jetty840/freelss/src/WebContent.cpp

/*
 ****************************************************************************
 *  Copyright (c) 2014 Uriah Liggett <freelaserscanner@gmail.com>           *
 *	This file is part of FreeLSS.                                           *
 *                                                                          *
 *  FreeLSS is free software: you can redistribute it and/or modify         *
 *  it under the terms of the GNU General Public License as published by    *
 *  the Free Software Foundation, either version 3 of the License, or       *
 *  (at your option) any later version.                                     *
 *                                                                          *
 *  FreeLSS is distributed in the hope that it will be useful,              *
 *  but WITHOUT ANY WARRANTY; without even the implied warranty of          *
 *  MERCHANTABILITY or FITNESS FOR A PARTICULAR PURPOSE.  See the           *
 *  GNU General Public License for more details.                            *
 *                                                                          *
 *   You should have received a copy of the GNU General Public License      *
 *   along with FreeLSS.  If not, see <http://www.gnu.org/licenses/>.       *
 ****************************************************************************
*/

#include "Main.h"
#include "WebContent.h"
#include "PresetManager.h"
#include "Setup.h"
#include "Laser.h"
#include "Camera.h"
#include "Progress.h"
#include "PlyWriter.h"
#include "Lighting.h"
#include "WifiConfig.h"

namespace freelss
{

// A warning is displayed if we have less than this amount of disk space available
const int WebContent::LOW_DISK_SPACE_MB = 1000;

const std::string WebContent::CSS = "\
<style type=\"text/css\">\
.menu2 {\
	float: left;\
	width: 650px;\
	height: 20px;\
    text-align: right;\
}\
body {\
	font-size: 20px;\
	font-family: Verdana, serif, Arial, Helvetica;\
	background-color: #aaa;\
	color: #ffffff;\
	text-shadow: #000000 2px 2px 2px;\
}\
A:link    {color: #ffffff; font-size: 22px; font-weight: bold; text-shadow: #000000 2px 2px 2px; text-decoration: none;}\
A:visited {color: #ffffff; font-size: 22px; font-weight: bold; text-shadow: #000000 2px 2px 2px; text-decoration: none;}\
A:hover   {color: #ffffff; font-size: 22px; font-weight: bold; text-shadow: #000000 2px 2px 2px; text-decoration: underline;}\
A:active  {color: #ffffff; font-size: 22px; font-weight: bold; text-shadow: #000000 2px 2px 2px; text-decoration: underline;}\
.submit {\
	height: 40px;\
	margin-bottom: 10px;\
	font-weight: bold;\
	font-size: 18px;\
	margin-right: 15px;\
}\
.controlSubmit {\
	width: 200px;\
	height: 40px;\
	margin-bottom: 10px;\
	font-weight: bold;\
	font-size: 18px;\
	margin-right: 15px;\
}\
.message {\
	text: rgb(255, 0, 0);\
	font-weight: bold;\
	font-size: 18px;\
}\
.submitContainer {\
	float: left;\
}\
.menu {\
	float: left;\
	width: 200px;\
	height: 30px;\
	background-color: #cae9ff;\
	border: solid 2px #1d5fa9;\
	padding-top: 10px;\
	padding-bottom: 5px;\
	margin-right: 20px;\
}\
.settingsText {\
	float: left;\
	width: 250px;\
}\
.settingsDescr{\
	font-size: 10px;\
	padding-bottom: 20px;\
}\
.settingsInput {\
	width: 150px;\
}\
.result {\
	margin-top: 10px;\
	padding-top: 10px;\
	padding-left: 10px;\
	display: inline-block;\
	vertical-align: middle;\
	background-color: rgb(200, 200, 200);\
	border: solid 2px #1d5fa9;\
	width: 625px;\
}\
.calDescr{\
	font-size: 10px;\
	padding-bottom: 20px;\
	width: 200px;\
}\
.cal1GenerateDebugDiv {\
	padding-bottom: 50px;\
}\
#deleteButton {\
	float: left;\
	padding-left: 10px;\
}\
#viewButton {\
	padding-left: 250px;\
}\
#error1 {\
	font-size: 40px;\
	font-family: Verdana, serif, Arial, Helvetica;\
	color: #ff0000;\
	text-shadow: #000000 2px 2px 2px;\
}\
#menuContainer {\
	width: 800px;\
	text-align: center;\
	padding-bottom: 50px;\
}\
#cal1ContentDiv {\
    margin-top: 75px;\
}\
#cal1ControlsDiv {\
	float: left;\
}\
#cal1ImageDiv {\
	float: none;\
	margin-top: 75px;\
}\
#outerImageDiv {\
	float: none;\
	margin-top: 75px;\
	width: 1296px;\
	height: 972px;\
	background-size: contain;\
	background-repeat: no-repeat;\
	background-image: url('skull.jpg');\
}\
#outerPresetDiv {\
	margin-top: 75px;\
	background-color: rgb(130, 130, 130);\
	width: 650px;\
	margin-bottom: 10px;\
	padding-top: 10px;\
}\
#presetTextDiv {\
	float: left;\
	padding-left: 25px;\
	padding-right: 12px;\
	padding-top: 5px;\
}\
</style>";

const std::string WebContent::JAVASCRIPT= "\
<script type=\"text/javascript\">\
var imageCount = 0;\
\
function endsWith(str, suffix) {\
    return str.indexOf(suffix, str.length - suffix.length) !== -1;\
}\
\
function startup1(){\
	setTimeout(updateImgImage, 1000);\
}\
function startup2(){\
	setTimeout(updateDivImage, 1000);\
}\
function updateImgImage(){\
	var img = document.getElementById('image');\
	img.src = 'camImageL_' + Math.random() + '.jpg';\
	imageCount = imageCount + 1;\
}\
function updateDivImage(){\
	var div = document.getElementById('outerImageDiv');\
	div.style.backgroundImage = \"url('camImageL_\" + Math.random() + \".jpg')\";\
	imageCount = imageCount + 1;\
	setTimeout(updateDivImage, 4000);\
}\
function centerTableClick(event)\
{\
	var pos_x = event.offsetX?(event.offsetX):event.pageX-document.getElementById('outerImageDiv').offsetLeft;\
	var pos_y = event.offsetY?(event.offsetY):event.pageY-document.getElementById('outerImageDiv').offsetTop;\
	window.location.href = 'cal3?y=' + pos_y;\
}\
function rightLaserClick(event) {\
    var pos_x = event.offsetX?(event.offsetX):event.pageX-document.getElementById('outerImageDiv').offsetLeft;\
    var pos_y = event.offsetY?(event.offsetY):event.pageY-document.getElementById('outerImageDiv').offsetTop;\
	window.location.href = 'cal4?rightLaserX=' + pos_x + '&rightLaserY=' + pos_y;\
}\
function leftLaserClick(event) {\
	var pos_x = event.offsetX?(event.offsetX):event.pageX-document.getElementById('outerImageDiv').offsetLeft;\
	var pos_y = event.offsetY?(event.offsetY):event.pageY-document.getElementById('outerImageDiv').offsetTop;\
	window.location.href = 'cal5?leftLaserX=' + pos_x + '&leftLaserY=' + pos_y;\
}\
</script>";

const std::string WebContent::PROFILE_NAME = "PROFILE_NAME";
const std::string WebContent::SERIAL_NUMBER = "SERIAL_NUMBER";
const std::string WebContent::CAMERA_X = "CAMERA_X";
const std::string WebContent::CAMERA_Y = "CAMERA_Y";
const std::string WebContent::CAMERA_Z = "CAMERA_Z";
const std::string WebContent::CAMERA_MODE = "CAMERA_MODE";
const std::string WebContent::RIGHT_LASER_X = "RIGHT_LASER_X";
const std::string WebContent::RIGHT_LASER_Y = "RIGHT_LASER_Y";
const std::string WebContent::RIGHT_LASER_Z = "RIGHT_LASER_Z";
const std::string WebContent::RIGHT_LASER_PIN = "RIGHT_LASER_PIN";
const std::string WebContent::LEFT_LASER_X = "LEFT_LASER_X";
const std::string WebContent::LEFT_LASER_Y = "LEFT_LASER_Y";
const std::string WebContent::LEFT_LASER_Z = "LEFT_LASER_Z";
const std::string WebContent::LEFT_LASER_PIN = "LEFT_LASER_PIN";
const std::string WebContent::LASER_MAGNITUDE_THRESHOLD = "LASER_MAGNITUDE_THRESHOLD";
const std::string WebContent::LASER_ON_VALUE = "LASER_ON_VALUE";
const std::string WebContent::LASER_SELECTION = "LASER_SELECTION";
const std::string WebContent::STABILITY_DELAY = "STABILITY_DELAY";
const std::string WebContent::MAX_LASER_WIDTH = "MAX_LASER_WIDTH";
const std::string WebContent::MIN_LASER_WIDTH = "MIN_LASER_WIDTH";
const std::string WebContent::STEPS_PER_REVOLUTION = "STEPS_PER_REVOLUTION";
const std::string WebContent::ENABLE_PIN = "ENABLE_PIN";
const std::string WebContent::STEP_PIN = "STEP_PIN";
const std::string WebContent::DIRECTION_PIN = "DIRECTION_PIN";
const std::string WebContent::DIRECTION_VALUE = "DIRECTION_VALUE";
const std::string WebContent::RESPONSE_DELAY = "RESPONSE_DELAY";
const std::string WebContent::STEP_DELAY = "STEP_DELAY";
const std::string WebContent::FRAMES_PER_REVOLUTION = "FRAMES_PER_REVOLUTION";
const std::string WebContent::GENERATE_XYZ = "GENERATE_XYZ";
const std::string WebContent::GENERATE_STL = "GENERATE_STL";
const std::string WebContent::GENERATE_PLY = "GENERATE_PLY";
const std::string WebContent::SEPARATE_LASERS_BY_COLOR = "SEPARATE_LASERS_BY_COLOR";
const std::string WebContent::UNIT_OF_LENGTH = "UNIT_OF_LENGTH";
const std::string WebContent::VERSION_NAME = "VERSION_NAME";
const std::string WebContent::GROUND_PLANE_HEIGHT = "GROUND_PLANE_HEIGHT";
const std::string WebContent::PLY_DATA_FORMAT = "PLY_DATA_FORMAT";
const std::string WebContent::FREE_DISK_SPACE = "FREE_DISK_SPACE";
const std::string WebContent::ENABLE_BURST_MODE = "ENABLE_BURST_MODE";
const std::string WebContent::ENABLE_LIGHTING = "ENABLE_LIGHTING";
const std::string WebContent::LIGHTING_TYPE = "LIGHTING_TYPE";
const std::string WebContent::LIGHTING_PIN = "LIGHTING_PIN";
const std::string WebContent::LIGHTING_ILLUMINATION_RGB = "LIGHTING_ILLUMINATION_RGB";
const std::string WebContent::LIGHTING_LASER_RGB = "LIGHTING_LASER_RGB";
const std::string WebContent::LIGHTING_NETWORK_INDICATION = "LIGHTING_NETWORK_INDICATION";
const std::string WebContent::LIGHTING_NETWORK_INTERFACE = "LIGHTING_NETWORK_INTERFACE";
const std::string WebContent::CREATE_BASE_FOR_OBJECT = "CREATE_BASE_FOR_OBJECT";
const std::string WebContent::WIFI_ESSID = "WIFI_ESSID";
const std::string WebContent::WIFI_ESSID_HIDDEN = "WIFI_ESSID_HIDDEN";
const std::string WebContent::WIFI_PASSWORD = "WIFI_PASSWORD";
const std::string WebContent::KERNEL_VERSION = "KERNEL_VERSION";
const std::string WebContent::ENABLE_AUTHENTICATION = "ENABLE_AUTHENTICATION";
const std::string WebContent::AUTH_USERNAME = "AUTH_USERNAME";
const std::string WebContent::AUTH_PASSWORD1 = "AUTH_PASSWORD1";
const std::string WebContent::AUTH_PASSWORD2 = "AUTH_PASSWORD2";
const std::string WebContent::MENU2 = "<div class=\"menu2\"><a href=\"/checkUpdate\"><small><small>Check for Update</small></small></a>&nbsp;&nbsp;&nbsp;&nbsp;<a href=\"/network\"><small><small>Network</small></small></a>&nbsp;&nbsp;&nbsp;&nbsp;<a href=\"/security\"><small><small>Security</small></small></a>&nbsp;&nbsp;&nbsp;&nbsp;<a href=\"/setup\"><small><small>Setup</small></small></a></div>";


const std::string WebContent::SERIAL_NUMBER_DESCR = "The serial number of the ATLAS 3D scanner";
const std::string WebContent::CAMERA_X_DESCR = "X-compoment of camera location. ie: The camera is always at X = 0.";
const std::string WebContent::CAMERA_Y_DESCR = "Y-component of camera location. ie: The distance from camera center to the XZ plane";
const std::string WebContent::CAMERA_Z_DESCR = "Z-component of camera location. ie: The distance from camera center to origin";
const std::string WebContent::RIGHT_LASER_X_DESCR = "X coordinate of the right laser.  This is how far the laser is from the camera.";
const std::string WebContent::RIGHT_LASER_Y_DESCR = "Y coordinate of the right laser";
const std::string WebContent::RIGHT_LASER_Z_DESCR = "Z coordinate of the right laser.  The laser is parallel with the camera focal point";
const std::string WebContent::LEFT_LASER_X_DESCR = "X coordinate of the right laser.  This is how far the laser is from the camera.";
const std::string WebContent::LEFT_LASER_Y_DESCR = "Y coordinate of the right laser";
const std::string WebContent::LEFT_LASER_Z_DESCR = "Z coordinate of the right laser.  The laser is parallel with the camera focal point";
const std::string WebContent::LASER_MAGNITUDE_THRESHOLD_DESCR = "How bright the difference between a laser on and laser off pixel must be in order to be detected as part of the laser";
const std::string WebContent::RIGHT_LASER_PIN_DESCR = "The wiringPi pin number for controlling the right laser";
const std::string WebContent::LEFT_LASER_PIN_DESCR = "The wiringPi pin number for controlling the left laser";
const std::string WebContent::LASER_ON_VALUE_DESCR = "Set to 1 if setting the laser pin HIGH turns if on and 0 if LOW turns it on";
const std::string WebContent::STABILITY_DELAY_DESCR = "The time in microseconds to delay after moving the turntable and before taking a picture";
const std::string WebContent::MAX_LASER_WIDTH_DESCR = "Maximum laser width in pixels";
const std::string WebContent::MIN_LASER_WIDTH_DESCR = "Minimum laser width in pixels";
const std::string WebContent::STEPS_PER_REVOLUTION_DESCR = "The number of motor steps before the turntable spins 360 degrees";
const std::string WebContent::ENABLE_PIN_DESCR = "The wiringPi pin number for enabling the stepper motor";
const std::string WebContent::STEP_PIN_DESCR = "The wiringPi pin number for stepping the stepper motor";
const std::string WebContent::STEP_DELAY_DESCR = "The amount of time between steps in microseconds";
const std::string WebContent::DIRECTION_PIN_DESCR = "The wiringPi pin number for the stepper motor direction or rotation";
const std::string WebContent::RESPONSE_DELAY_DESCR = "The time it takes for the stepper controller to recognize a pin value change in microseconds";
const std::string WebContent::FRAMES_PER_REVOLUTION_DESCR = "The number of frames that should be taken for a scan. Default is 800.";
const std::string WebContent::GENERATE_XYZ_DESCR = "Whether to generate an XYZ point cloud file from the scan.";
const std::string WebContent::GENERATE_STL_DESCR = "Whether to generate an STL mesh from the scan.";
const std::string WebContent::GENERATE_PLY_DESCR = "Whether to generate a PLY point clould from the scan.";
const std::string WebContent::SEPARATE_LASERS_BY_COLOR_DESCR = "Calibration debugging option to separate the results from different lasers by color (requires PLY).";
const std::string WebContent::GROUND_PLANE_HEIGHT_DESCR = "Any scan data less than this height above the turntable will not be included in the output files.";
const std::string WebContent::PLY_DATA_FORMAT_DESCR = "Whether to generate binary or ASCII PLY files.";
const std::string WebContent::ENABLE_BURST_MODE_DESCR = "Enables the camera's burst mode when capturing in still mode";
const std::string WebContent::ENABLE_LIGHTING_DESCR = "Enables support for controlling a connected light.";
const std::string WebContent::LIGHTING_PIN_DESCR = "For type PWM, use The wiringPi pin number for the light. For type WS281x use the GPIO number (typically 18). Change will not go into effect until system is rebooted.";
const std::string WebContent::LIGHTING_ILLUMINATION_RGB_DESCR = "The RGB value used to illuminate the model when lasers are off during scanning, used for coloring the object.  Format RRGGBB (hex).  For type PWM; RR, GG and BB should be the same are represent intensity.";
const std::string WebContent::LIGHTING_LASER_RGB_DESCR = "The RGB value used to illuminate the model when lasers are on during scanning.  Format RRGGBB (hex).  For type PWM; RR, GG and BB should be the same are represent intensity.";
const std::string WebContent::CREATE_BASE_FOR_OBJECT_DESCR = "Adds a flat base to the object for easier 3D printing preparation.";
const std::string WebContent::WIFI_ESSID_DESCR = "The wireless network to configure";
const std::string WebContent::WIFI_PASSWORD_DESCR = "The password for the wireless network";
const std::string WebContent::ENABLE_AUTHENTICATION_DESCR = "Enables password protection for accessing the scanner";
const std::string WebContent::AUTH_USERNAME_DESCR = "The username to login with";
const std::string WebContent::AUTH_PASSWORD1_DESCR = "The password to login with";
const std::string WebContent::AUTH_PASSWORD2_DESCR = "Repeat the password";

std::string WebContent::scan(const std::vector<ScanResult>& pastScans)
{
	const Preset& preset = PresetManager::get()->getActivePreset();
	std::string presetName = preset.name;

	std::stringstream sstr;
	sstr << "<!DOCTYPE html><html><head>"
		 << CSS
		 << std::endl
		 << JAVASCRIPT
		 << std::endl
		 << "</head>"
	     << "\
<body>\
<div id=\"menuContainer\">\
  <div class=\"menu\"><a href=\"/\">SCAN</a></div>\
  <div class=\"menu\"><a href=\"/cal1\">CAMERA</a></div>\
  <div class=\"menu\"><a href=\"/settings\">SETTINGS</a></div>\
</div>\
<p>Click the button to start the scan </p>\
<form action=\"/\" method=\"POST\" enctype=\"application/x-www-form-urlencoded\">\
<div><div class=\"settingsText\">Preset</div><input class=\"settingsInput\" readonly=\"true\" value=\"" << presetName << "\"></div>\
<div><div class=\"settingsText\">Range</div><input name=\"degrees\" class=\"settingsInput\" value=\"360\"> degrees</div>\
	<input type=\"hidden\" name=\"cmd\" value=\"startScan\">\
	<input class=\"submit\" type=\"submit\" value=\"Start Scan\">\
</form>";

	int diskSpaceMb = GetFreeSpaceMb();
	if (diskSpaceMb < WebContent::LOW_DISK_SPACE_MB)
	{
		sstr << "<div id=\"error1\">LOW DISK SPACE WARNING: " << diskSpaceMb << " MB</div>";
	}

	for (size_t iRt = 0; iRt < pastScans.size(); iRt++)
	{
		sstr << WebContent::scanResult(iRt + 1, pastScans[iRt]);
	}

	sstr << "</body></html>";

	return sstr.str();
}

std::string WebContent::scanResult(size_t index, const ScanResult& result)
{
	std::stringstream sstr;

	time_t scanDate = result.getScanDate();

	struct tm * tp = localtime (&scanDate);
	std::string dateStr = asctime(tp);
	std::stringstream deleteUrl;

	std::stringstream thumbnail;
	thumbnail << "/dl/" << result.getScanDate() << ".png";
	deleteUrl << "/del?id=" << result.getScanDate();

	sstr << "<span>" << index << "\
	<div class=\"result\">\
	<div style=\"float: left\">\
	<img width=\"128\" border=\"0\" src=\"" << thumbnail.str() << "\">\
	</div>";

	bool hasPly = false;
	const std::vector<ScanResultFile>& files = result.files;
	for (size_t iFil = 0; iFil < files.size(); iFil++)
	{
		const ScanResultFile& file = files[iFil];
		if (file.extension != "png")
		{
			std::string upperExtension = file.extension;
			std::transform(upperExtension.begin(), upperExtension.end(), upperExtension.begin(), toupper);

			// Format the file size
			std::stringstream fileSize;
			if (file.fileSize > 1024 * 1024)
			{
				fileSize << file.fileSize / (1024 * 1024) << " MB";
			}
			else if (file.fileSize > 1024)
			{
				fileSize << file.fileSize / 1024 << " KB";
			}
			else
			{
				fileSize << file.fileSize << " B";
			}

			sstr << "&nbsp;<a href=\"/dl/" << result.getScanDate()
				 << "." << file.extension << "\">"
				 << upperExtension << "</a><small>&nbsp;["
				 << fileSize.str() << "]</small>";
		}

		if (file.extension == "ply")
		{
			hasPly = true;
		}
	}

	sstr << "<br><br>\
	<div id=\"deleteButton\"><form action=\"" << deleteUrl.str() << "#\" method=\"POST\">\
	<input type=\"Submit\" value=\"Delete\">\
	</form></div>";

	// Show the PLY view link
	if (hasPly)
	{
		sstr << "<div id=\"viewButton\"><form action=\"/view\" method=\"POST\" enctype=\"application/x-www-form-urlencoded\">"
			 << "<input type=\"Hidden\" name=\"id\" value=\"" << result.getScanDate() << "\">"
			 << "<input style=\"left-padding: 20px\" type=\"Submit\" value=\"View\">"
			 << "</form></div>";
	}

	sstr << "<div style=\"font-size: 12px\">" << dateStr << "\
	</div></div>\
	</span>\
	<br>";

	return sstr.str();
}

std::string WebContent::scanRunning(Progress& progress, real remainingTime)
{
	real minRemaining = remainingTime / 60.0;

	std::stringstream sstr;
	sstr << "<!DOCTYPE html><html><head>"
		 << "<meta http-equiv=\"refresh\" content=\"5\">"
		 << CSS
		 << std::endl
		 << JAVASCRIPT
		 << std::endl
		 << "</head>"
	     << "<body><p><div style=\"float: left\">"
	     << progress.getLabel()
	     << " is "
	     << progress.getPercent()
	     << "% complete";

		if (minRemaining > 0.01)
		{
			 sstr << " with "
				  << minRemaining
				  << " minutes remaining";
		}

	sstr << ".&nbsp;</div><div style=\"padding-left: 50px\"><form action=\"/preview\" method=\"GET\" enctype=\"application/x-www-form-urlencoded\">"
		 << "<input type=\"submit\" value=\"Preview\">"
		 << "</form></div><br><br>"
	     << "<form action=\"/\" method=\"POST\" enctype=\"application/x-www-form-urlencoded\">"
	     << "<input type=\"hidden\" name=\"cmd\" value=\"stopScan\">"
	     << "<input type=\"submit\" value=\"Stop Scan\">"
	     << "</form>"
	     << "</body></html>";

	     return sstr.str();
}

std::string WebContent::viewScan(const std::string& plyFilename)
{
	std::stringstream sstr;
	sstr << "<!DOCTYPE html><html><head>"
		 << CSS
		 << std::endl
		 << JAVASCRIPT
		 << std::endl
		 << "\
		 </head><body>\
		 <div style=\"position: absolute; left: 10px; top: 10px\"> <a href=\"/\">Back</a>&nbsp;&nbsp;<a href=\"/preview\">Refresh</a></div>\
		 <script src=\"three.min.js\"></script>\
		 <script src=\"OrbitControls.js\"></script>\
		 <script src=\"PLYLoader.js\"></script>\
		 <script>\
		 var scene = new THREE.Scene();\
		var camera = new THREE.PerspectiveCamera( 30, window.innerWidth/window.innerHeight, 1.0, 10000 );\
		var controls;\
\
		var renderer = new THREE.WebGLRenderer({ alpha: true });\
		renderer.setSize( window.innerWidth, window.innerHeight );\
		renderer.setClearColor( 0x555555, 1);\
\
		document.body.appendChild( renderer.domElement );\
		window.addEventListener( 'resize', onWindowResize, false );\
\
		var loader = new THREE.PLYLoader();\
		loader.addEventListener( 'load', function ( event ) {\
			var geometry = event.content;\
			var pcMaterial = new THREE.PointCloudMaterial( {\
			size: 1.75,\
			vertexColors: THREE.VertexColors\
		} );\
			geometry.useColor = true;\
			var mesh = new THREE.PointCloud( geometry, pcMaterial );\
			scene.add( mesh );\
		} );";

		sstr << "loader.load( '" << plyFilename << "');";

		sstr << "\
		var cylHeight = 1;\
		var cylRadius = 6 * 25.4;\
		var cylGeometry = new THREE.CylinderGeometry( cylRadius, cylRadius, cylHeight, 64 );\
		var cylMaterial = new THREE.MeshBasicMaterial( {color: 0x222222 } );\
		var cylinder = new THREE.Mesh( cylGeometry, cylMaterial );\
		cylinder.translateY( -cylHeight/2 );\
		scene.add( cylinder );\
\
		var cylHeight2 = 8;\
		var cylRadius2 = 6 * 25.4;\
		var cylGeometry2 = new THREE.CylinderGeometry( cylRadius2, cylRadius2, cylHeight2, 64 );\
		var cylMaterial2 = new THREE.MeshBasicMaterial( { color: 0xaaaaaa } );\
		var cylinder2 = new THREE.Mesh( cylGeometry2, cylMaterial2 );\
		cylinder2.translateY( -cylHeight2/2 - cylHeight );\
		scene.add( cylinder2 );\
\
		camera.position.z = 350;\
		camera.position.y = 450;\
		controls = new THREE.OrbitControls( camera );\
		controls.maxDistance = 1000;\
\
		var render = function () {\
			requestAnimationFrame( render );\
			renderer.render(scene, camera);\
		};\
\
		render();\
\
		function onWindowResize() {\
			windowHalfX = window.innerWidth / 2;\
			windowHalfY = window.innerHeight / 2;\
			camera.aspect = window.innerWidth / window.innerHeight;\
			camera.updateProjectionMatrix();\
			renderer.setSize( window.innerWidth, window.innerHeight );\
		}\
	</script>";

	sstr << "</body></html>";

	return sstr.str();
}

std::string WebContent::cal1(const std::string& inMessage)
{
	std::string message = inMessage.empty() ? std::string("") : ("<h2>" + inMessage + "</h2>");

	std::stringstream sstr;
	sstr << "<!DOCTYPE html><html><head>"
		 << CSS
		 << std::endl
		 << JAVASCRIPT
		 << std::endl
		 << "</head>"
	     << "\
<body onload=\"startup1();\">\
<div id=\"menuContainer\">\
  <div class=\"menu\"><a href=\"/\">SCAN</a></div>\
  <div class=\"menu\"><a href=\"/cal1\">CAMERA</a></div>\
  <div class=\"menu\"><a href=\"/settings\">SETTINGS</a></div>\
</div>"
	     << message
         << "\
<div id=\"cal1ContentDiv\">\
  <div id=\"cal1ControlsDiv\">\
    <div class=\"cal1GenerateDebugDiv\">\
		<form action=\"/cal1\" method=\"POST\" enctype=\"application/x-www-form-urlencoded\">\
			<input name=\"cmd\" value=\"generateDebug\" type=\"hidden\">\
			<input style=\"height: 60px\" class=\"controlSubmit\" value=\"Test\" type=\"submit\">\
		</form>\
    </div>\
    <div class=\"cal1GenerateDebugDiv\">\
        <form action=\"/cal1\" method=\"POST\" enctype=\"application/x-www-form-urlencoded\"><input name=\"cmd\" value=\"calibrateLasers\" type=\"hidden\"><input class=\"controlSubmit\" value=\"Calibrate Lasers\" type=\"submit\"></form>\
        <div class=\"calDescr\">Line the front wall of the calibration item over the center of the turntable hole and click this button to calibrate the lasers.</div>\
    </div>";

	sstr << "\
	<form action=\"/cal1\" method=\"POST\" enctype=\"application/x-www-form-urlencoded\"><input name=\"cmd\" value=\"toggleLeftLaser\" type=\"hidden\"><input class=\"controlSubmit\" value=\"Toggle Left Laser\" type=\"submit\"></form>\
	<form action=\"/cal1\" method=\"POST\" enctype=\"application/x-www-form-urlencoded\"> <input name=\"cmd\" value=\"toggleRightLaser\" type=\"hidden\"> <input class=\"controlSubmit\" value=\"Toggle Right Laser\" type=\"submit\"> </form>\
	<form action=\"/cal1\" method=\"POST\" enctype=\"application/x-www-form-urlencoded\">  <input name=\"cmd\" value=\"disableMotor\" type=\"hidden\">  <input class=\"controlSubmit\" value=\"Disable Motor\" type=\"submit\">  </form>\
	<div>\
		<form action=\"/cal1\" method=\"POST\" enctype=\"application/x-www-form-urlencoded\">\
		<input name=\"cmd\" value=\"rotateTable\" type=\"hidden\">\
		<input name=\"degrees\" style=\"width: 75px\" class=\"settingsInput\" value=\"360\" type=\"text\">\
		<input class=\"submit\" style=\"width: 110px\" value=\"Rotate\" type=\"submit\">\
		</form>\
	</div>\
	<div class=\"calDescr\">Rotates the turntable in degrees.</div>\
  </div>\
<div style=\"position: relative\">\
	<div>\
		<img style=\"position: absolute\" onload=\"setTimeout(updateImgImage, 0);\" id=\"image\" width=\"1296\" src=\"camImageL_\""
	<< time(NULL)
	<< ".jpg\">\
	</div>\
</div>\
</div></body></html>";

	     return sstr.str();
}

std::string WebContent::showUpdate(SoftwareUpdate * update, const std::string& message)
{
	std::stringstream sstr;
	sstr << "<!DOCTYPE html><html><head>"
		 << CSS
		 << std::endl
		 << JAVASCRIPT
		 << std::endl
		 << "</head>"
		 << "\
<body>\
<div id=\"menuContainer\">\
  <div class=\"menu\"><a href=\"/\">SCAN</a></div>\
  <div class=\"menu\"><a href=\"/cal1\">CAMERA</a></div>\
  <div class=\"menu\"><a href=\"/settings\">SETTINGS</a></div>"
		 << WebContent::MENU2
		 << "\
</div><div style=\"padding-top: 50px\">";

	if (update != NULL)
	{
		sstr << "<p>Update Available: " << update->name << "</p>";
		sstr << "<div><form action=\"/applyUpdate\" method=\"POST\" enctype=\"application/x-www-form-urlencoded\">";
		sstr <<" <input type=\"submit\" name=\"applyUpdate\" value=\"Apply Update\">";
		sstr <<" <input type=\"hidden\" name=\"majorVersion\" value=\"" << update->majorVersion << "\">";
		sstr <<" <input type=\"hidden\" name=\"minorVersion\" value=\"" << update->minorVersion << "\">";
		sstr << "</form></div>";
	}
	else if (!message.empty())
	{
		sstr << "<h2>" << message << "</h2>";
	}
	else
	{
		sstr << "<h2>No updates available.</h2>";
	}

	sstr << "</div></body></html>";

	return sstr.str();
}

std::string WebContent::updateApplied(SoftwareUpdate * update, const std::string& message, bool success)
{
	std::stringstream sstr;
	sstr << "<!DOCTYPE html><html><head>"
		 << CSS
		 << std::endl
		 << JAVASCRIPT
		 << std::endl
		 << "</head>"
		 << "\
<body>\
<div id=\"menuContainer\">\
  <div class=\"menu\"><a href=\"/\">SCAN</a></div>\
  <div class=\"menu\"><a href=\"/cal1\">CAMERA</a></div>\
  <div class=\"menu\"><a href=\"/settings\">SETTINGS</a></div>"
		 << WebContent::MENU2
		 << "\
</div><div style=\"padding-top: 50px\">";

	sstr << "<h2>" << message << "</h2>";

	sstr << "</div></body></html>";

	return sstr.str();
}

std::string WebContent::security(const std::string& message)
{
	Setup * setup = Setup::get();

	std::stringstream sstr;
	sstr << "<!DOCTYPE html><html><head>"
		 << CSS
		 << std::endl
		 << JAVASCRIPT
		 << std::endl
		 << "</head>"
		 << "\
<body>\
<div id=\"menuContainer\">\
  <div class=\"menu\"><a href=\"/\">SCAN</a></div>\
  <div class=\"menu\"><a href=\"/cal1\">CAMERA</a></div>\
  <div class=\"menu\"><a href=\"/settings\">SETTINGS</a></div>"
		 << WebContent::MENU2
		 << "\
</div><div style=\"padding-top: 50px\">";

	if (!message.empty())
	{
		sstr << "<h2>" << message << "</h2>";
	}

	sstr << "<form action=\"/security\" method=\"POST\" enctype=\"application/x-www-form-urlencoded\">";
	sstr << checkbox(WebContent::ENABLE_AUTHENTICATION, "Require Password", setup->enableAuthentication, ENABLE_AUTHENTICATION_DESCR);
	sstr << setting(WebContent::AUTH_USERNAME, "Username", "pi", AUTH_USERNAME_DESCR,  "", true);
	sstr << setting(WebContent::AUTH_PASSWORD1, "Password", "", AUTH_PASSWORD1_DESCR,  "", false, true);
	sstr << setting(WebContent::AUTH_PASSWORD2, "Repeat Password", "", AUTH_PASSWORD2_DESCR,  "", false, true);
	sstr << "<p><input type=\"hidden\" name=\"cmd\" value=\"save\">\
<input class=\"submit\" type=\"submit\" value=\"Save\">\
</p></form></div>\
</body></html>";

	return sstr.str();
}
std::string WebContent::network(const std::string& message, bool hiddenEssidInput)
{
	WifiConfig * wifi = WifiConfig::get();

	//  Perform a scan
	if (!hiddenEssidInput)
	{
		wifi->scan();
	}

	std::vector<std::string> interfaces = wifi->getAllInterfaces();
	std::vector<WifiConfig::AccessPoint> accessPoints = wifi->getAccessPoints();

	std::stringstream sstr;
	sstr << "<!DOCTYPE html><html><head>"
		 << CSS
		 << std::endl
		 << JAVASCRIPT
		 << std::endl
		 << "</head>"
		 << "\
<body>\
<div id=\"menuContainer\">\
  <div class=\"menu\"><a href=\"/\">SCAN</a></div>\
  <div class=\"menu\"><a href=\"/cal1\">CAMERA</a></div>\
  <div class=\"menu\"><a href=\"/settings\">SETTINGS</a></div>"
		 << WebContent::MENU2
		 << "\
</div><div style=\"padding-top: 50px\">";

	if (!message.empty())
	{
		sstr << "<h2>" << message << "</h2>";
	}

	sstr << "<form action=\"/network\" method=\"POST\" enctype=\"application/x-www-form-urlencoded\">";

	for (size_t iNt = 0; iNt < interfaces.size(); iNt++)
	{
		std::string interface = interfaces[iNt];
		if (interface != "lo")
		{
			sstr << setting(interface, interface, wifi->getIpAddress(interface), "IP address for " + interface, "", true);
		}
	}

	if (!hiddenEssidInput)
	{
		sstr << "<div><div class=\"settingsText\">Wireless Network</div>";
		sstr << "<select name=\"" << WebContent::WIFI_ESSID << "\">";
		for (size_t iAp = 0; iAp < accessPoints.size(); iAp++)
		{
			sstr << "<option value=\"" << iAp << "\">" << accessPoints[iAp].essid << "</option>\r\n";
		}

		sstr << "</select>&nbsp;&nbsp;<a href=\"?hidden=true\"><small><small>Hidden</small></small></a></div>";

		sstr << "";
		sstr << "<div class=\"settingsDescr\">" << WIFI_ESSID_DESCR << "</div>\n";
	}
	else
	{
		sstr << setting(WebContent::WIFI_ESSID_HIDDEN, "Wireless Network", "", WIFI_ESSID_DESCR);
	}

	sstr << setting(WebContent::WIFI_PASSWORD, "Wireless Password", "", WIFI_PASSWORD_DESCR);
	sstr << "<p><input type=\"hidden\" name=\"cmd\" value=\"connect\">\
<input class=\"submit\" type=\"submit\" value=\"Connect\">\
</p></form></div>\
</body></html>";

	return sstr.str();
}

std::string WebContent::setup(const std::string& message)
{
	const Setup * setup = Setup::get();
	UnitOfLength srcUnit = UL_MILLIMETERS; // Lengths are always represented in millimeters internally
	UnitOfLength dstUnit = setup->unitOfLength;

	// Detect the amount of free space available
	std::string freeSpaceMb = ToString(GetFreeSpaceMb());

	std::stringstream kernelVersion;
	struct utsname uts;

	if (uname(&uts) == 0)
	{
		kernelVersion << uts.sysname << " " << uts.release << " " << uts.version << " " << uts.machine;
	}

	std::stringstream sstr;
	sstr << "<!DOCTYPE html><html><head>"
		 << CSS
		 << std::endl
		 << JAVASCRIPT
		 << std::endl
		 << "</head>"
	     << "\
<body>\
<div id=\"menuContainer\">\
  <div class=\"menu\"><a href=\"/\">SCAN</a></div>\
  <div class=\"menu\"><a href=\"/cal1\">CAMERA</a></div>\
  <div class=\"menu\"><a href=\"/settings\">SETTINGS</a></div>"
	     << WebContent::MENU2
	     << "\
</div><div style=\"padding-top: 50px\">";

	if (!message.empty())
	{
		sstr << "<h2>" << message << "</h2>";
	}

	sstr << "<form action=\"/setup\" method=\"POST\" enctype=\"application/x-www-form-urlencoded\">";
	sstr << "<p><input class=\"submit\" type=\"submit\" value=\"Save\"></p>";

	sstr << setting(WebContent::SERIAL_NUMBER, "Serial Number", setup->serialNumber, SERIAL_NUMBER_DESCR);

	std::string mmSel = setup->unitOfLength == UL_MILLIMETERS ? " SELECTED" : "";
	std::string cmSel = setup->unitOfLength == UL_CENTIMETERS ? " SELECTED" : "";
	std::string inSel = setup->unitOfLength == UL_INCHES ? " SELECTED" : "";

	sstr << "<div><div class=\"settingsText\">Unit of Length</div>";
	sstr << "<select name=\"" << WebContent::UNIT_OF_LENGTH << "\">";
	sstr << "<option value=\"1\"" << mmSel << ">Millimeters</option>\r\n";
	sstr << "<option value=\"3\"" << cmSel << ">Centimeters</option>\r\n";
	sstr << "<option value=\"2\"" << inSel << ">Inches</option>\r\n";
	sstr << "</select></div>";
	sstr << "<div class=\"settingsDescr\">The unit of length for future values entered on the setup page.</div>\n";

	sstr << setting(WebContent::CAMERA_X, "Camera X", ConvertUnitOfLength(setup->cameraLocation.x, srcUnit, dstUnit), CAMERA_X_DESCR, ToString(dstUnit) + ".", true);
	sstr << setting(WebContent::CAMERA_Y, "Camera Y", ConvertUnitOfLength(setup->cameraLocation.y, srcUnit, dstUnit), CAMERA_Y_DESCR,  ToString(dstUnit) + ".");
	sstr << setting(WebContent::CAMERA_Z, "Camera Z", ConvertUnitOfLength(setup->cameraLocation.z, srcUnit, dstUnit), CAMERA_Z_DESCR,  ToString(dstUnit) + ".");
	sstr << setting(WebContent::RIGHT_LASER_X, "Right Laser X", ConvertUnitOfLength(setup->rightLaserLocation.x, srcUnit, dstUnit), RIGHT_LASER_X_DESCR,  ToString(dstUnit) + ".");
	sstr << setting(WebContent::RIGHT_LASER_Y, "Right Laser Y", ConvertUnitOfLength(setup->rightLaserLocation.y, srcUnit, dstUnit), RIGHT_LASER_Y_DESCR,  ToString(dstUnit) + ".", true);
	sstr << setting(WebContent::RIGHT_LASER_Z, "Right Laser Z", ConvertUnitOfLength(setup->rightLaserLocation.z, srcUnit, dstUnit), RIGHT_LASER_Z_DESCR,  ToString(dstUnit) + ".", true);
	sstr << setting(WebContent::LEFT_LASER_X, "Left Laser X", ConvertUnitOfLength(setup->leftLaserLocation.x, srcUnit, dstUnit), LEFT_LASER_X_DESCR,  ToString(dstUnit) + ".");
	sstr << setting(WebContent::LEFT_LASER_Y, "Left Laser Y", ConvertUnitOfLength(setup->leftLaserLocation.y, srcUnit, dstUnit), LEFT_LASER_Y_DESCR,  ToString(dstUnit) + ".", true);
	sstr << setting(WebContent::LEFT_LASER_Z, "Left Laser Z", ConvertUnitOfLength(setup->leftLaserLocation.z, srcUnit, dstUnit), LEFT_LASER_Z_DESCR,  ToString(dstUnit) + ".", true);

	sstr << setting(WebContent::RIGHT_LASER_PIN, "Right Laser Pin", setup->rightLaserPin, RIGHT_LASER_PIN_DESCR);
	sstr << setting(WebContent::LEFT_LASER_PIN, "Left Laser Pin", setup->leftLaserPin, LEFT_LASER_PIN_DESCR);
	sstr << setting(WebContent::LASER_ON_VALUE, "Laser On Value", setup->laserOnValue, LASER_ON_VALUE_DESCR);

	sstr << setting(WebContent::STEPS_PER_REVOLUTION, "Steps Per Revolution", setup->stepsPerRevolution, STEPS_PER_REVOLUTION_DESCR);
	sstr << setting(WebContent::ENABLE_PIN, "Motor Enable Pin", setup->motorEnablePin, ENABLE_PIN_DESCR);
	sstr << setting(WebContent::STEP_PIN, "Motor Step Pin", setup->motorStepPin, STEP_PIN_DESCR);
	sstr << setting(WebContent::STEP_DELAY, "Motor Step Delay", setup->motorStepDelay, STEP_DELAY_DESCR, "&mu;s");
	sstr << setting(WebContent::DIRECTION_PIN, "Motor Direction Pin", setup->motorDirPin, DIRECTION_PIN_DESCR);
	sstr << setting(WebContent::RESPONSE_DELAY, "Motor Response Delay", setup->motorResponseDelay, RESPONSE_DELAY_DESCR, "&mu;s");
	sstr << checkbox(WebContent::ENABLE_LIGHTING, "Enable Lighting", setup->enableLighting, ENABLE_LIGHTING_DESCR);

	std::string pwmSel = setup->lightingType == LT_PWM ? " SELECTED" : "";
	std::string ws281xSel = setup->lightingType == LT_WS281X ? " SELECTED" : "";

	sstr << "<div><div class=\"settingsText\">Lighting Type</div>";
	sstr << "<select name=\"" << WebContent::LIGHTING_TYPE << "\">";
	sstr << "<option value=\"1\"" << pwmSel << ">PWM</option>\r\n";
	sstr << "<option value=\"2\"" << ws281xSel << ">WS281x</option>\r\n";
	sstr << "</select></div>";
	sstr << "<div class=\"settingsDescr\">The type of lighting installed.  WS281x is also known as Neopixel.</div>\n";

	sstr << setting(WebContent::LIGHTING_PIN, "Lighting Pin", setup->lightingPin, LIGHTING_PIN_DESCR);
	sstr << setting(WebContent::LIGHTING_ILLUMINATION_RGB, "Lighting Illumination RGB", setup->lightingIlluminationRGB, LIGHTING_ILLUMINATION_RGB_DESCR);
	sstr << setting(WebContent::LIGHTING_LASER_RGB, "Lighting Laser RGB", setup->lightingLaserRGB, LIGHTING_LASER_RGB_DESCR);

	std::string offSel = setup->lightingNetworkIndication == LN_OFF ? " SELECTED" : "";
	std::string fullSel = setup->lightingNetworkIndication == LN_FULL ? " SELECTED" : "";
	std::string lastSel = setup->lightingNetworkIndication == LN_LAST ? " SELECTED" : "";

	sstr << "<div><div class=\"settingsText\">Lighting Network IP Indication</div>";
	sstr << "<select name=\"" << WebContent::LIGHTING_NETWORK_INDICATION << "\">";
	sstr << "<option value=\"1\"" << offSel << ">Off</option>\r\n";
	sstr << "<option value=\"2\"" << fullSel << ">Full</option>\r\n";
	sstr << "<option value=\"3\"" << lastSel << ">Last</option>\r\n";
	sstr << "</select></div>";
	sstr << "<div class=\"settingsDescr\">Indicates the IP address by an LED count or flashing the lighting when freelss is started.  Full is the full ip address, Last is the last number of the address.</div>\n";

        WifiConfig * wifi = WifiConfig::get();
        std::vector<std::string> interfaces = wifi->getAllInterfaces();

	sstr << "<div><div class=\"settingsText\">Lighting Network Interface</div>";
	sstr << "<select name=\"" << WebContent::LIGHTING_NETWORK_INTERFACE << "\">";
	for (size_t iNt = 0; iNt < interfaces.size(); iNt++)
	{
		std::string selected;
		std::string interface = interfaces[iNt];
		if (interface != "lo")
		{
			selected = (interface == setup->lightingNetworkInterface) ? " SELECTED" : "";
			sstr << "<option value=\"" << interface << "\"" << selected << ">" << interface << "</option>\r\n";
		}
	}
	sstr << "</select></div>";
	sstr << "<div class=\"settingsDescr\">The interface to be indicated.</div>\n";

	sstr << setting(WebContent::VERSION_NAME, "Firmware Version", FREELSS_VERSION_NAME, "The version of FreeLSS the scanner is running", "", true);
	sstr << setting(WebContent::FREE_DISK_SPACE, "Free Space", freeSpaceMb, "The amount of free disk space available", "MB", true);
	sstr << setting(WebContent::KERNEL_VERSION, "Kernel", kernelVersion.str(), "The version of the kernel", "", true);


	sstr << "<p><input type=\"hidden\" name=\"cmd\" value=\"save\">\
<input class=\"submit\" type=\"submit\" value=\"Save\">\
</p></form></div>\
</body></html>";

	     return sstr.str();
}

std::string WebContent::settings(const std::string& message)
{
	const Setup * setup = Setup::get();
	UnitOfLength srcUnit = UL_MILLIMETERS; // Lengths are always represented in millimeters internally
	UnitOfLength dstUnit = setup->unitOfLength;

	const Preset& preset = PresetManager::get()->getActivePreset();

	std::stringstream sstr;
	sstr << "<!DOCTYPE html><html><head>"
		 << CSS
		 << std::endl
		 << JAVASCRIPT
		 << std::endl
		 << "</head>"
	     << "\
<body>\
<div id=\"menuContainer\">\
  <div class=\"menu\"><a href=\"/\">SCAN</a></div>\
  <div class=\"menu\"><a href=\"/cal1\">CAMERA</a></div>\
  <div class=\"menu\"><a href=\"/settings\">SETTINGS</a></div>"
	     << WebContent::MENU2
	     << "</div>";

	if (!message.empty())
	{
		sstr << "<h2>" << message << "</h2>";
	}


	sstr << "<form action=\"/settings\" method=\"POST\" enctype=\"application/x-www-form-urlencoded\">";

	sstr << "\
	<div id=\"outerPresetDiv\">\
		<div id=\"presetTextDiv\">Preset</div>\
		<div style=\"float: left\"><input name=\""
		<< WebContent::PROFILE_NAME
		<< "\" value=\""
		<< preset.name
		<< "\" type=\"text\"></div>\
<div style=\"padding-left: 10px; float: left\"><input name=\"cmd\" class=\"submit\" value=\"Save\" type=\"submit\"></div>\
<div style=\"padding-left: 0px\"><input name=\"cmd\" class=\"submit\" value=\"Delete\" type=\"submit\"></div>";

	const std::vector<Preset>& profs = PresetManager::get()->getPresets();
	for (size_t iProf = 0; iProf < profs.size(); iProf++)
	{
		const Preset& prof = profs[iProf];

		sstr << "<div style=\"padding-left: 10px; padding-bottom: 10px\">"
		     << "<div style=\"width: 500px\">"
		     << (iProf + 1)
		     << ".<a href=\"/settings?cmd=activate&id="
		     << prof.id
		     << "\">&nbsp;&nbsp;"
		     << prof.name
		     << "</a></div>"
		     << "</div>";
	}

	sstr << "</div>";

	//
	// Laser selection UI
	//
	Laser::LaserSide laserSel = preset.laserSide;
	std::string leftSel  = laserSel == Laser::LEFT_LASER  ? " SELECTED" : "";
	std::string rightSel = laserSel == Laser::RIGHT_LASER ? " SELECTED" : "";
	std::string bothSel  = laserSel == Laser::ALL_LASERS  ? " SELECTED" : "";

	sstr << "<div><div class=\"settingsText\">Laser Selection</div>";
	sstr << "<select name=\"" << WebContent::LASER_SELECTION << "\">";
	sstr << "<option value=\"0\"" << leftSel << ">Left Laser</option>\r\n";
	sstr << "<option value=\"1\"" << rightSel << ">Right Laser</option>\r\n";
	sstr << "<option value=\"2\"" << bothSel << ">Both Lasers</option>\r\n";
	sstr << "</select></div>";
	sstr << "<div class=\"settingsDescr\">The laser(s) that will be used when scanning.</div>\n";


	//
	// Camera Mode UI
	//
	Camera::CameraMode cameraMode = preset.cameraMode;
	std::string still5Sel   = cameraMode == Camera::CM_STILL_5MP  ? " SELECTED" : "";
	std::string video5Sel   = cameraMode == Camera::CM_VIDEO_5MP ? " SELECTED" : "";
	std::string videoHDSel  = cameraMode == Camera::CM_VIDEO_HD ? " SELECTED" : "";
	std::string video1P2Sel = cameraMode == Camera::CM_VIDEO_1P2MP ? " SELECTED" : "";
	std::string videoVGASel = cameraMode == Camera::CM_VIDEO_VGA ? " SELECTED" : "";

	sstr << "<div><div class=\"settingsText\">Camera Mode</div>";
	sstr << "<select name=\"" << WebContent::CAMERA_MODE<< "\">";
	sstr << "<option value=\"" << (int)Camera::CM_STILL_5MP << "\"" << still5Sel << ">5 Megapixel (still mode, 2592x1944)</option>\r\n";
	sstr << "<option value=\"" << (int)Camera::CM_VIDEO_5MP << "\"" << video5Sel << ">5 Megapixel (video mode, 2592x1944)</option>\r\n";
	sstr << "<option value=\"" << (int)Camera::CM_VIDEO_HD << "\"" << videoHDSel << ">1.9 Megapixel (video mode, 1600x1200)</option>\r\n";
	sstr << "<option value=\"" << (int)Camera::CM_VIDEO_1P2MP << "\"" << video1P2Sel << ">1.2 Megapixel (video mode, 1280x960)</option>\r\n";
	sstr << "<option value=\"" << (int)Camera::CM_VIDEO_VGA << "\"" << videoVGASel << ">0.3 Megapixel (video mode, 640x480)</option>\r\n";
	sstr << "</select></div>";
	sstr << "<div class=\"settingsDescr\">The camera mode to use. Video mode is faster but Still mode results in higher quality scans.</div>\n";

	sstr << setting(WebContent::FRAMES_PER_REVOLUTION, "Frames Per Revolution", preset.framesPerRevolution, FRAMES_PER_REVOLUTION_DESCR);
	sstr << setting(WebContent::LASER_MAGNITUDE_THRESHOLD, "Laser Threshold", preset.laserThreshold, LASER_MAGNITUDE_THRESHOLD_DESCR);
	sstr << setting(WebContent::GROUND_PLANE_HEIGHT, "Ground Plane Height", ConvertUnitOfLength(preset.groundPlaneHeight, srcUnit, dstUnit), GROUND_PLANE_HEIGHT_DESCR,  ToString(dstUnit) + ".", false);
	sstr << setting(WebContent::STABILITY_DELAY, "Stability Delay", preset.stabilityDelay, STABILITY_DELAY_DESCR, "&mu;s");
	sstr << setting(WebContent::MAX_LASER_WIDTH, "Max Laser Width", preset.maxLaserWidth, MAX_LASER_WIDTH_DESCR, "px.");
	sstr << setting(WebContent::MIN_LASER_WIDTH, "Min Laser Width", preset.minLaserWidth, MIN_LASER_WIDTH_DESCR, "px.");


	//
	// PLY Data Format UI
	//
	PlyDataFormat plyDataFormat = preset.plyDataFormat;
	std::string plyAsciiSel  = plyDataFormat == PLY_ASCII  ? " SELECTED" : "";
	std::string plyBinarySel = plyDataFormat == PLY_BINARY ? " SELECTED" : "";

	sstr << checkbox(WebContent::GENERATE_PLY, "Generate PLY File", preset.generatePly, GENERATE_PLY_DESCR);

	sstr << "<div><div class=\"settingsText\">PLY Data Format</div>";
	sstr << "<select name=\"" << WebContent::PLY_DATA_FORMAT << "\">";
	sstr << "<option value=\"0\"" << plyAsciiSel << ">ASCII</option>\r\n";
	sstr << "<option value=\"1\"" << plyBinarySel << ">Binary</option>\r\n";
	sstr << "</select></div>";
	sstr << "<div class=\"settingsDescr\">" << WebContent::PLY_DATA_FORMAT_DESCR << "</div>\n";

	sstr << checkbox(WebContent::GENERATE_STL, "Generate STL File", preset.generateStl, GENERATE_STL_DESCR);
	sstr << checkbox(WebContent::GENERATE_XYZ, "Generate XYZ File", preset.generateXyz, GENERATE_XYZ_DESCR);
	sstr << checkbox(WebContent::SEPARATE_LASERS_BY_COLOR, "Separate the Lasers", preset.laserMergeAction == Preset::LMA_SEPARATE_BY_COLOR, SEPARATE_LASERS_BY_COLOR_DESCR);
	sstr << checkbox(WebContent::ENABLE_BURST_MODE, "Enable Burst Mode", preset.enableBurstModeForStillImages, ENABLE_BURST_MODE_DESCR);
	sstr << checkbox(WebContent::CREATE_BASE_FOR_OBJECT, "Create Base for Object", preset.createBaseForObject, CREATE_BASE_FOR_OBJECT_DESCR);

	sstr << "<p><br><br><a target=\"_\" href=\"/licenses.txt\">Licenses</a></p>";
	sstr << "</form>\
	<form action=\"/reboot\" method=\"POST\" enctype=\"application/x-www-form-urlencoded\">\
	<p><br><br><br><input class=\"submit\" type=\"submit\" value=\"Reboot\"></p></form>";

	sstr << "</form>\
<form action=\"/settings\" method=\"POST\" enctype=\"application/x-www-form-urlencoded\">\
<p><br><br><br><form> <input type=\"hidden\" name=\"cmd\" value=\"shutdown\">\
<input class=\"submit\" type=\"submit\" value=\"Shutdown\"></p></form>";

	sstr << "</body></html>";

	     return sstr.str();
}

std::string WebContent::setting(const std::string& name, const std::string& label,
			const std::string& value, const std::string& description, const std::string& units, bool readOnly, bool password)
{
	std::stringstream sstr;
	sstr << "<div><div class=\"settingsText\">"
		 << label
		 << "</div>";

	if (!readOnly)
	{
		sstr << "<input class=\"settingsInput\" value=\""
			 << value
			 << "\" name=\""
			 << name
			 << "\" ";

		if (readOnly)
		{
			sstr << "readonly=\"true\"";
		}

		if (password)
		{
			sstr << " type=\"password\"";
		}

		sstr << "> ";

		if (!units.empty())
		{
			sstr << units;
		}
	}
	else
	{
		sstr << "<div><small>" << value << "</small> ";

		if (!units.empty())
		{
			sstr << units;
		}
		sstr << "</div>";
	}

	sstr << "</div><div class=\"settingsDescr\">" << description << "</div>\n";


	return sstr.str();
}

std::string WebContent::checkbox(const std::string& name, const std::string& label, bool checked, const std::string& description)
{
	std::stringstream sstr;
	sstr << "<div><div class=\"settingsText\">"
		 << label
		 << "</div><input class=\"settingsInput\" name=\""
		 << name
		 << "\" type=\"checkbox\"";

	if (checked)
	{
		sstr << " checked";
	}

	sstr << "> ";

	sstr << "</div><div class=\"settingsDescr\">" << description << "</div>\n";


	return sstr.str();
}

std::string WebContent::setting(const std::string& name, const std::string& label,
		int value, const std::string& description, const std::string& units, bool readOnly)
{
	std::stringstream sstr;
	sstr << value;
	return setting(name, label, sstr.str(), description, units, readOnly);
}

std::string WebContent::setting(const std::string& name, const std::string& label,
		uint32_t value, const std::string& description, const std::string& units, bool readOnly)
{
	std::string str = ToString(value);
	return setting(name, label, str, description, units, readOnly);
}

std::string WebContent::setting(const std::string& name, const std::string& label,
		real value, const std::string& description, const std::string& units, bool readOnly)
{
	std::stringstream sstr;
	sstr << value;
	return setting(name, label, sstr.str(), description, units, readOnly);
}

}
